akovcharova/GEM_scripts/in/HIROSE_FX10A_140S_14_SV.dxf

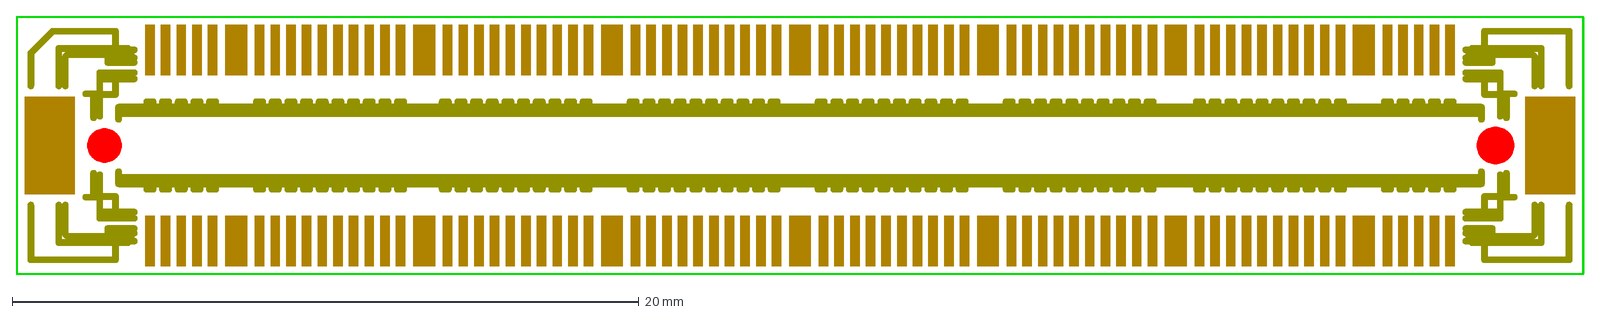
[picture p12: CAD file, 2018-05-09]
in/HIROSE_FX10A_140S_14_SV.dxf
50.1 x 8.25 mm
